emnyeca/emiuet/firmware/main/midi_out_uart_trs.c

#include "midi_out.h"

#include <stddef.h>

#include "board_pins.h"
#include "sdkconfig.h"

/* Defensive defaults for newly introduced Kconfig symbols.
 * This prevents build failures when the build directory has a stale sdkconfig.h.
 * Defaults must match Kconfig.projbuild.
 */
#ifndef CONFIG_EMIUET_MIDI_TRS_UART_ENABLE
#define CONFIG_EMIUET_MIDI_TRS_UART_ENABLE 0
#endif

#ifndef CONFIG_EMIUET_MIDI_TRS_IN_ENABLE
#define CONFIG_EMIUET_MIDI_TRS_IN_ENABLE 0
#endif

#ifndef CONFIG_EMIUET_MIDI_TASK_TRS_PRIORITY
#define CONFIG_EMIUET_MIDI_TASK_TRS_PRIORITY 7
#endif

#ifndef CONFIG_EMIUET_MIDI_TRS_QUEUE_LEN
#define CONFIG_EMIUET_MIDI_TRS_QUEUE_LEN 64
#endif

#include "esp_log.h"

#include "driver/uart.h"
#include "freertos/FreeRTOS.h"
#include "freertos/task.h"
#include "freertos/queue.h"
#include "midi_input.h"

static const char *TAG = "midi_out_uart_trs";

/*
 * TRS MIDI (Type-A) backend
 *
 * - UART: 31250 bps, 8-N-1
 * - Hardware is responsible for MIDI electrical compliance.
 *
 * Rev.B maps both Type-A TRS directions to UART1 through the GPIO matrix.
 */

#define MIDI_TRS_UART_PORT       UART_NUM_1
#define MIDI_TRS_UART_BAUDRATE   31250

#define MIDI_TRS_COALESCE_CHANNELS 16

typedef struct {
    uint8_t len;
    uint8_t bytes[3];
} midi_tx_item_t;

static bool s_inited = false;
static bool s_enabled = false;
static QueueHandle_t s_q = NULL;
static TaskHandle_t s_task = NULL;
static TaskHandle_t s_rx_task = NULL;
static midi_input_parser_t s_rx_parser;
static portMUX_TYPE s_coalesce_mux = portMUX_INITIALIZER_UNLOCKED;

/* Coalesce state (per-channel) */
static bool s_pb_pending[MIDI_TRS_COALESCE_CHANNELS] = {0};
static uint8_t s_pb_lsb[MIDI_TRS_COALESCE_CHANNELS] = {0};
static uint8_t s_pb_msb[MIDI_TRS_COALESCE_CHANNELS] = {0};

static bool s_cc1_pending[MIDI_TRS_COALESCE_CHANNELS] = {0};
static uint8_t s_cc1_val[MIDI_TRS_COALESCE_CHANNELS] = {0};

/* Stats */
static uint32_t s_drop_queue = 0;
static uint32_t s_drop_write = 0;
static uint32_t s_coalesce_pb = 0;
static uint32_t s_coalesce_cc1 = 0;
static uint32_t s_q_hwm = 0;
static TickType_t s_last_stats_log_tick = 0;

static inline void maybe_update_hwm(void)
{
    if (!s_q) return;
    const UBaseType_t used = uxQueueMessagesWaiting(s_q);
    if (used > s_q_hwm) s_q_hwm = (uint32_t)used;
}

static void maybe_log_stats(void)
{
    const TickType_t now = xTaskGetTickCount();
    const TickType_t interval = pdMS_TO_TICKS(1000);
    if (s_last_stats_log_tick != 0 && (now - s_last_stats_log_tick) < interval) return;

    if (s_drop_queue || s_drop_write || s_coalesce_pb || s_coalesce_cc1) {
        ESP_LOGW(TAG,
                 "stats q_hwm=%lu drop{q=%lu write=%lu} coalesce{pb=%lu cc1=%lu}",
                 (unsigned long)s_q_hwm,
                 (unsigned long)s_drop_queue,
                 (unsigned long)s_drop_write,
                 (unsigned long)s_coalesce_pb,
                 (unsigned long)s_coalesce_cc1);
    }
    s_last_stats_log_tick = now;
}

static inline bool is_pitchbend_3(const uint8_t *b, size_t len)
{
    return (len == 3) && ((b[0] & 0xF0u) == 0xE0u);
}

static inline bool is_cc1_3(const uint8_t *b, size_t len)
{
    return (len == 3) && ((b[0] & 0xF0u) == 0xB0u) && ((b[1] & 0x7Fu) == 1u);
}

static bool trs_uart_write_bytes(const uint8_t *bytes, size_t len)
{
    if (!bytes || len == 0) return false;
    int written = uart_write_bytes(MIDI_TRS_UART_PORT, (const char *)bytes, len);
    return written == (int)len;
}

static void trs_flush_coalesced_once(void)
{
    /* Flush coalesced continuous values. We keep this bounded and quick. */
    for (int ch = 0; ch < MIDI_TRS_COALESCE_CHANNELS; ++ch) {
        bool pb = false;
        uint8_t pb_lsb = 0;
        uint8_t pb_msb = 0;

        portENTER_CRITICAL(&s_coalesce_mux);
        pb = s_pb_pending[ch];
        if (pb) {
            pb_lsb = s_pb_lsb[ch];
            pb_msb = s_pb_msb[ch];
            s_pb_pending[ch] = false;
        }
        portEXIT_CRITICAL(&s_coalesce_mux);

        if (pb) {
            uint8_t b[3] = {(uint8_t)(0xE0u | (uint8_t)ch), pb_lsb, pb_msb};
            if (!trs_uart_write_bytes(b, sizeof(b))) {
                s_drop_write++;
            }
        }

        bool cc1 = false;
        uint8_t cc1_v = 0;

        portENTER_CRITICAL(&s_coalesce_mux);
        cc1 = s_cc1_pending[ch];
        if (cc1) {
            cc1_v = s_cc1_val[ch];
            s_cc1_pending[ch] = false;
        }
        portEXIT_CRITICAL(&s_coalesce_mux);

        if (cc1) {
            uint8_t b[3] = {(uint8_t)(0xB0u | (uint8_t)ch), 1u, (uint8_t)(cc1_v & 0x7Fu)};
            if (!trs_uart_write_bytes(b, sizeof(b))) {
                s_drop_write++;
            }
        }
    }
}

/* Producers publish (enqueue or coalesce) before notifying. The sender drains
 * everything before waiting again, so a notification given during a drain stays
 * pending and the next wait returns at once: no wakeup is lost.
 */
static inline void trs_tx_wake(void)
{
    TaskHandle_t task = s_task;
    if (task) xTaskNotifyGive(task);
}

static void trs_sender_task(void *arg)
{
    (void)arg;

    /* We intentionally do not call uart_wait_tx_done() per message.
     * UART driver TX buffer + this dedicated task provides stable latency.
     * uart_write_bytes() waits for ring-buffer space, so there is no retry state.
     */
    const int FLUSH_EVERY_N_EVENTS = 8;

    for (;;) {
        int sent_since_flush = 0;
        midi_tx_item_t item = {0};

        /* Single sender task owns the UART; no mutex required. */
        while (s_q && xQueueReceive(s_q, &item, 0) == pdTRUE) {
            maybe_update_hwm();
            if (!trs_uart_write_bytes(item.bytes, item.len)) {
                s_drop_write++;
            }
            if (++sent_since_flush >= FLUSH_EVERY_N_EVENTS) {
                sent_since_flush = 0;
                trs_flush_coalesced_once();
            }
        }

        /* Queue empty: flush continuous updates promptly, then sleep until notified. */
        trs_flush_coalesced_once();
        maybe_log_stats();
        (void)ulTaskNotifyTake(pdTRUE, portMAX_DELAY);
    }
}

static void trs_receiver_task(void *arg)
{
    (void)arg;
    uint8_t data[64];
    for (;;) {
        const int count = uart_read_bytes(MIDI_TRS_UART_PORT, data, sizeof(data),
                                          pdMS_TO_TICKS(20));
        if (count > 0) midi_input_feed(&s_rx_parser, data, (size_t)count);
    }
}

bool midi_out_uart_trs_init(void)
{
    if (s_inited) return s_enabled;
    s_inited = true;

#if !CONFIG_EMIUET_MIDI_TRS_UART_ENABLE
    s_enabled = false;
    ESP_LOGI(TAG, "TRS UART backend disabled (CONFIG_EMIUET_MIDI_TRS_UART_ENABLE=n)");
    return false;
#else

    uart_config_t cfg = {
        .baud_rate = MIDI_TRS_UART_BAUDRATE,
        .data_bits = UART_DATA_8_BITS,
        .parity = UART_PARITY_DISABLE,
        .stop_bits = UART_STOP_BITS_1,
        .flow_ctrl = UART_HW_FLOWCTRL_DISABLE,
        .source_clk = UART_SCLK_DEFAULT,
    };

    esp_err_t err = uart_param_config(MIDI_TRS_UART_PORT, &cfg);
    if (err != ESP_OK) {
        s_enabled = false;
        ESP_LOGE(TAG, "uart_param_config failed: %s", esp_err_to_name(err));
        return false;
    }

    err = uart_set_pin(MIDI_TRS_UART_PORT,
                       (int)PIN_MIDI_OUT_TX,
                       CONFIG_EMIUET_MIDI_TRS_IN_ENABLE ? (int)PIN_MIDI_IN_RX : UART_PIN_NO_CHANGE,
                       UART_PIN_NO_CHANGE,
                       UART_PIN_NO_CHANGE);
    if (err != ESP_OK) {
        s_enabled = false;
        ESP_LOGE(TAG, "uart_set_pin failed: %s", esp_err_to_name(err));
        return false;
    }

    /* A single UART driver owns both isolated MIDI IN and compliant MIDI OUT. */
    err = uart_driver_install(MIDI_TRS_UART_PORT, 256, 512, 0, NULL, 0);
    if (err != ESP_OK) {
        s_enabled = false;
        ESP_LOGE(TAG, "uart_driver_install failed: %s", esp_err_to_name(err));
        return false;
    }

    s_q = xQueueCreate(CONFIG_EMIUET_MIDI_TRS_QUEUE_LEN, sizeof(midi_tx_item_t));
    if (s_q == NULL) {
        s_enabled = false;
        ESP_LOGE(TAG, "failed to create queue");
        return false;
    }

    if (s_task == NULL) {
        BaseType_t ok = xTaskCreatePinnedToCore(trs_sender_task,
                                               "midi_trs_tx",
                                               4096,
                                               NULL,
                                               CONFIG_EMIUET_MIDI_TASK_TRS_PRIORITY,
                                               &s_task,
                                               0);
        if (ok != pdPASS) {
            s_task = NULL;
            s_enabled = false;
            ESP_LOGE(TAG, "failed to create sender task");
            return false;
        }
    }

#if CONFIG_EMIUET_MIDI_TRS_IN_ENABLE
    midi_input_parser_init(&s_rx_parser);
    if (s_rx_task == NULL) {
        BaseType_t ok = xTaskCreatePinnedToCore(trs_receiver_task,
                                               "midi_trs_rx",
                                               3072,
                                               NULL,
                                               CONFIG_EMIUET_MIDI_TASK_TRS_PRIORITY,
                                               &s_rx_task,
                                               0);
        if (ok != pdPASS) {
            ESP_LOGE(TAG, "failed to create receiver task");
            return false;
        }
    }
#endif

    s_enabled = true;
    ESP_LOGI(TAG, "TRS UART backend initialized (port=%d tx=%d rx=%d baud=%d)",
             (int)MIDI_TRS_UART_PORT, (int)PIN_MIDI_OUT_TX,
             CONFIG_EMIUET_MIDI_TRS_IN_ENABLE ? (int)PIN_MIDI_IN_RX : -1,
             (int)MIDI_TRS_UART_BAUDRATE);
    return true;
#endif
}

bool midi_out_uart_trs_send_bytes(const uint8_t *bytes, size_t len)
{
    if (!s_enabled) return false;
    if (!bytes || len == 0) return false;

    /* Coalesce continuous controllers to prevent queue saturation. */
    if (is_pitchbend_3(bytes, len)) {
        const uint8_t ch = (uint8_t)(bytes[0] & 0x0Fu);
        portENTER_CRITICAL(&s_coalesce_mux);
        if (s_pb_pending[ch]) s_coalesce_pb++;
        s_pb_pending[ch] = true;
        s_pb_lsb[ch] = (uint8_t)(bytes[1] & 0x7Fu);
        s_pb_msb[ch] = (uint8_t)(bytes[2] & 0x7Fu);
        portEXIT_CRITICAL(&s_coalesce_mux);
        trs_tx_wake();
        return true;
    }

    if (is_cc1_3(bytes, len)) {
        const uint8_t ch = (uint8_t)(bytes[0] & 0x0Fu);
        portENTER_CRITICAL(&s_coalesce_mux);
        if (s_cc1_pending[ch]) s_coalesce_cc1++;
        s_cc1_pending[ch] = true;
        s_cc1_val[ch] = (uint8_t)(bytes[2] & 0x7Fu);
        portEXIT_CRITICAL(&s_coalesce_mux);
        trs_tx_wake();
        return true;
    }

    if (!s_q) return false;
    midi_tx_item_t item = {0};
    item.len = (uint8_t)((len > 3) ? 3 : len);
    for (size_t i = 0; i < item.len; ++i) item.bytes[i] = bytes[i];

    if (xQueueSendToBack(s_q, &item, 0) != pdTRUE) {
        s_drop_queue++;
        maybe_update_hwm();
        trs_tx_wake();
        return false;
    }

    maybe_update_hwm();
    trs_tx_wake();
    return true;
}
