emnyeca/emiuet/firmware/main/midi_out_usb.c

#include "midi_out.h"

#include <stddef.h>
#include <string.h>

#include "esp_log.h"
#include "input_router.h"
#include "midi_input.h"
#include "usb_hid_keyboard.h"
#include "usb_power.h"

/* Defensive defaults for newly introduced Kconfig symbols.
 * This prevents build failures when the build directory has a stale sdkconfig.h.
 * Defaults must match Kconfig.projbuild.
 */
#ifndef CONFIG_EMIUET_MIDI_USB_QUEUE_LEN
#define CONFIG_EMIUET_MIDI_USB_QUEUE_LEN 1024
#endif

#ifndef CONFIG_EMIUET_MIDI_TASK_USB_PRIORITY
#define CONFIG_EMIUET_MIDI_TASK_USB_PRIORITY 6
#endif

#include "freertos/FreeRTOS.h"
#include "freertos/task.h"
#include "freertos/queue.h"
#include "freertos/semphr.h"

static const char *TAG = "midi_out_usb";

/*
 * Fixed-role USB Device backend
 *
 * This is intentionally isolated behind a config gate so the project
 * still builds even when TinyUSB is not enabled in sdkconfig.
 */
#if defined(CONFIG_TINYUSB_MIDI_COUNT) && (CONFIG_TINYUSB_MIDI_COUNT > 0)

#include "tinyusb.h"
#include "tinyusb_default_config.h"
#include "tusb.h"
#include "class/midi/midi_device.h"

/* Some TinyUSB versions (including the one bundled via ESP-IDF 5.3.x managed component)
 * don't provide tud_midi_ready(). Provide a local shim so we can log the state using the
 * name requested, without changing descriptors or the send path.
 */
static inline bool tud_midi_ready(void)
{
    return tud_midi_mounted();
}

#ifndef EMUIET_USB_MIDI_VID
#define EMUIET_USB_MIDI_VID 0x303A /* Espressif VID (commonly used in examples) */
#endif

#ifndef EMUIET_USB_MIDI_PID
#define EMUIET_USB_MIDI_PID 0x4005
#endif

#ifndef EMUIET_USB_MIDI_BCD
#define EMUIET_USB_MIDI_BCD 0x0101
#endif

/* USB descriptors */
static const tusb_desc_device_t s_desc_device = {
    .bLength = sizeof(tusb_desc_device_t),
    .bDescriptorType = TUSB_DESC_DEVICE,
    .bcdUSB = 0x0200,

    .bDeviceClass = 0x00,
    .bDeviceSubClass = 0x00,
    .bDeviceProtocol = 0x00,

    /* 64B is valid for Full Speed EP0 and avoids relying on tusb_config.h */
    .bMaxPacketSize0 = 64,

    .idVendor = EMUIET_USB_MIDI_VID,
    .idProduct = EMUIET_USB_MIDI_PID,
    .bcdDevice = EMUIET_USB_MIDI_BCD,

    .iManufacturer = 0x01,
    .iProduct = 0x02,
    .iSerialNumber = 0x03,

    .bNumConfigurations = 0x01,
};

/* Strings must remain in flash/ROM */
static const char *s_string_desc[] = {
    (const char[]){0x09, 0x04}, /* 0: English (0x0409) */
    "Emnyeca",
    "Emiuet MIDI + Keyboard",
    "0001",
    "Emiuet Keyboard",
};

/*
 * Configuration descriptor:
 * - One configuration
 * - MIDI 1.0 function (Audio Control + MIDI Streaming interfaces)
 * - HID boot keyboard interface
 */
#define EMUIET_USB_ITF_NUM_MIDI 0
#define EMUIET_USB_ITF_NUM_HID  2
#define EMUIET_USB_ITF_NUM_TOTAL 3

#define EMUIET_USB_EP_MIDI_OUT 0x01
#define EMUIET_USB_EP_MIDI_IN  0x81
#define EMUIET_USB_EP_HID_IN   0x82

#ifndef EMUIET_USB_MIDI_EP_SIZE
#define EMUIET_USB_MIDI_EP_SIZE 64
#endif

#ifndef EMUIET_USB_HID_EP_SIZE
#define EMUIET_USB_HID_EP_SIZE 8
#endif

static const uint8_t s_hid_report_descriptor[] = {
    TUD_HID_REPORT_DESC_KEYBOARD()
};

static const uint8_t s_desc_configuration[] = {
    TUD_CONFIG_DESCRIPTOR(1, EMUIET_USB_ITF_NUM_TOTAL, 0,
                          (TUD_CONFIG_DESC_LEN + TUD_MIDI_DESC_LEN + TUD_HID_DESC_LEN),
                          0x00, 500),
    /* Note: TUD_MIDI_DESCRIPTOR signature depends on TinyUSB version. In esp-idf v5.3.4's tinyusb, it is:
     *   TUD_MIDI_DESCRIPTOR(itfnum, stridx, epout, epin, epsize)
     * We don't provide a dedicated interface string, so stridx=0.
     */
    TUD_MIDI_DESCRIPTOR(EMUIET_USB_ITF_NUM_MIDI, 0, EMUIET_USB_EP_MIDI_OUT, EMUIET_USB_EP_MIDI_IN, EMUIET_USB_MIDI_EP_SIZE),
    TUD_HID_DESCRIPTOR(EMUIET_USB_ITF_NUM_HID, 4, HID_ITF_PROTOCOL_KEYBOARD,
                       sizeof(s_hid_report_descriptor), EMUIET_USB_EP_HID_IN,
                       EMUIET_USB_HID_EP_SIZE, 10)
};

static bool s_inited = false;
static midi_input_parser_t s_midi_rx_parser;
static TaskHandle_t s_usb_state_task_handle = NULL;

typedef struct {
    uint8_t len;
    uint8_t bytes[3];
} midi_tx_item_t;

static QueueHandle_t s_usb_q = NULL;
static TaskHandle_t s_usb_tx_task_handle = NULL;
static portMUX_TYPE s_usb_coalesce_mux = portMUX_INITIALIZER_UNLOCKED;

static bool s_usb_pb_pending[16] = {0};
static uint8_t s_usb_pb_lsb[16] = {0};
static uint8_t s_usb_pb_msb[16] = {0};

static bool s_usb_cc1_pending[16] = {0};
static uint8_t s_usb_cc1_val[16] = {0};

static uint32_t s_usb_drop_queue = 0;
static uint32_t s_usb_drop_write = 0;
static uint32_t s_usb_coalesce_pb = 0;
static uint32_t s_usb_coalesce_cc1 = 0;
static uint32_t s_usb_q_hwm = 0;
static TickType_t s_usb_last_stats_log_tick = 0;

uint8_t const *tud_hid_descriptor_report_cb(uint8_t instance)
{
    (void)instance;
    return s_hid_report_descriptor;
}

void tud_midi_rx_cb(uint8_t instance)
{
    (void)instance;
    uint8_t bytes[64];
    while (tud_midi_available()) {
        const uint32_t count = tud_midi_stream_read(bytes, sizeof(bytes));
        if (count == 0) break;
        midi_input_feed(&s_midi_rx_parser, bytes, count);
    }
}

uint16_t tud_hid_get_report_cb(uint8_t instance, uint8_t report_id,
                               hid_report_type_t report_type, uint8_t *buffer,
                               uint16_t reqlen)
{
    (void)instance;
    (void)report_id;
    (void)report_type;
    (void)buffer;
    (void)reqlen;
    return 0;
}

void tud_hid_set_report_cb(uint8_t instance, uint8_t report_id,
                           hid_report_type_t report_type,
                           uint8_t const *buffer, uint16_t bufsize)
{
    (void)instance;
    (void)report_id;
    if (report_type == HID_REPORT_TYPE_OUTPUT && buffer && bufsize > 0) {
        usb_hid_keyboard_set_led_report(buffer[0]);
    }
}

static void usb_clear_pending_midi(void)
{
    if (s_usb_q) (void)xQueueReset(s_usb_q);
    portENTER_CRITICAL(&s_usb_coalesce_mux);
    memset(s_usb_pb_pending, 0, sizeof(s_usb_pb_pending));
    memset(s_usb_cc1_pending, 0, sizeof(s_usb_cc1_pending));
    portEXIT_CRITICAL(&s_usb_coalesce_mux);
}

static inline void usb_maybe_update_hwm(void)
{
    if (!s_usb_q) return;
    const UBaseType_t used = uxQueueMessagesWaiting(s_usb_q);
    if (used > s_usb_q_hwm) s_usb_q_hwm = (uint32_t)used;
}

static void usb_maybe_log_stats(void)
{
    const TickType_t now = xTaskGetTickCount();
    const TickType_t interval = pdMS_TO_TICKS(1000);
    if (s_usb_last_stats_log_tick != 0 && (now - s_usb_last_stats_log_tick) < interval) return;

    if (s_usb_drop_queue || s_usb_drop_write || s_usb_coalesce_pb || s_usb_coalesce_cc1) {
        ESP_LOGW(TAG,
                 "stats q_hwm=%lu drop{q=%lu write=%lu} coalesce{pb=%lu cc1=%lu}",
                 (unsigned long)s_usb_q_hwm,
                 (unsigned long)s_usb_drop_queue,
                 (unsigned long)s_usb_drop_write,
                 (unsigned long)s_usb_coalesce_pb,
                 (unsigned long)s_usb_coalesce_cc1);
    }
    s_usb_last_stats_log_tick = now;
}

static inline bool is_pitchbend_3(const uint8_t *b, size_t len)
{
    return (len == 3) && ((b[0] & 0xF0u) == 0xE0u);
}

static inline bool is_cc1_3(const uint8_t *b, size_t len)
{
    return (len == 3) && ((b[0] & 0xF0u) == 0xB0u) && ((b[1] & 0x7Fu) == 1u);
}

static bool usb_send_lowlevel(const uint8_t *bytes, size_t len)
{
    if (!s_inited) return false;
    if (!bytes || len == 0) return false;
    if (!tud_mounted()) return false;

    uint32_t written = tud_midi_stream_write(0, bytes, (uint32_t)len);
    return written == len;
}

/* Producers publish (enqueue or coalesce) before notifying. The sender drains
 * everything before waiting again, so a notification given during a drain stays
 * pending and the next wait returns at once: no wakeup is lost.
 */
static inline void usb_tx_wake(void)
{
    TaskHandle_t task = s_usb_tx_task_handle;
    if (task) xTaskNotifyGive(task);
}

/* Returns false when TinyUSB could not accept a value; it stays pending. */
static bool usb_flush_coalesced_once(void)
{
    for (int ch = 0; ch < 16; ++ch) {
        bool pb = false;
        uint8_t pb_lsb = 0;
        uint8_t pb_msb = 0;

        portENTER_CRITICAL(&s_usb_coalesce_mux);
        pb = s_usb_pb_pending[ch];
        if (pb) {
            pb_lsb = s_usb_pb_lsb[ch];
            pb_msb = s_usb_pb_msb[ch];
            s_usb_pb_pending[ch] = false;
        }
        portEXIT_CRITICAL(&s_usb_coalesce_mux);

        if (pb) {
            uint8_t b[3] = {(uint8_t)(0xE0u | (uint8_t)ch), pb_lsb, pb_msb};
            if (!usb_send_lowlevel(b, sizeof(b))) {
                /* Keep pending on failure to avoid losing latest value. */
                portENTER_CRITICAL(&s_usb_coalesce_mux);
                /* A producer may have published a newer value during I/O. */
                if (!s_usb_pb_pending[ch]) {
                    s_usb_pb_pending[ch] = true;
                    s_usb_pb_lsb[ch] = pb_lsb;
                    s_usb_pb_msb[ch] = pb_msb;
                }
                portEXIT_CRITICAL(&s_usb_coalesce_mux);
                s_usb_drop_write++;
                return false;
            }
        }

        bool cc1 = false;
        uint8_t cc1_v = 0;

        portENTER_CRITICAL(&s_usb_coalesce_mux);
        cc1 = s_usb_cc1_pending[ch];
        if (cc1) {
            cc1_v = s_usb_cc1_val[ch];
            s_usb_cc1_pending[ch] = false;
        }
        portEXIT_CRITICAL(&s_usb_coalesce_mux);

        if (cc1) {
            uint8_t b[3] = {(uint8_t)(0xB0u | (uint8_t)ch), 1u, (uint8_t)(cc1_v & 0x7Fu)};
            if (!usb_send_lowlevel(b, sizeof(b))) {
                portENTER_CRITICAL(&s_usb_coalesce_mux);
                if (!s_usb_cc1_pending[ch]) {
                    s_usb_cc1_pending[ch] = true;
                    s_usb_cc1_val[ch] = cc1_v;
                }
                portEXIT_CRITICAL(&s_usb_coalesce_mux);
                s_usb_drop_write++;
                return false;
            }
        }
    }
    return true;
}

/* Sends queued discrete events in order, interleaving the coalesced values every
 * USB_FLUSH_EVERY_N_EVENTS and after the queue empties. Returns false if TinyUSB
 * refused data (TX FIFO full or not mounted); that data stays pending.
 * A refused 1-3 byte message is not partially written: TinyUSB checks for a free
 * 4-byte packet before consuming any byte, and this task is the only writer.
 */
#define USB_FLUSH_EVERY_N_EVENTS 16

static bool usb_tx_drain(int *sent_since_flush)
{
    midi_tx_item_t item = {0};
    while (s_usb_q && xQueuePeek(s_usb_q, &item, 0) == pdTRUE) {
        /* Preserve the interleave deadline across FIFO-full retries. */
        if (*sent_since_flush >= USB_FLUSH_EVERY_N_EVENTS) {
            if (!usb_flush_coalesced_once()) return false;
            *sent_since_flush = 0;
        }
        usb_maybe_update_hwm();
        if (!usb_send_lowlevel(item.bytes, item.len)) {
            s_usb_drop_write++;
            return false;
        }
        (void)xQueueReceive(s_usb_q, &item, 0);
        ++*sent_since_flush;
    }
    if (!usb_flush_coalesced_once()) return false;
    *sent_since_flush = 0;
    return true;
}

/* On refusal, actually block for a tick so the lower-priority TinyUSB task can
 * free TX space. Producer notifications must not bypass this scheduling break.
 */
#define USB_TX_RETRY_TICKS (pdMS_TO_TICKS(1) ? pdMS_TO_TICKS(1) : (TickType_t)1)

static void midi_out_usb_tx_task(void *arg)
{
    (void)arg;
    int sent_since_flush = 0;
    for (;;) {
        const bool drained = usb_tx_drain(&sent_since_flush);
        usb_maybe_log_stats();
        if (drained) {
            (void)ulTaskNotifyTake(pdTRUE, portMAX_DELAY);
        } else {
            vTaskDelay(USB_TX_RETRY_TICKS);
        }
    }
}

static void midi_out_usb_event_cb(tinyusb_event_t *event, void *arg)
{
    (void)arg;
    if (!event) return;

    switch (event->id) {
        case TINYUSB_EVENT_ATTACHED:
            /* Only the state monitor grants Default-current RGB power, so a
             * failed monitor task cannot leave an unmonitored grant active. */
            ESP_LOGI(TAG, "tud_mount_cb(): tud_mounted()=%d tud_midi_ready()=%d", (int)tud_mounted(), (int)tud_midi_ready());
            usb_tx_wake();
            break;
        case TINYUSB_EVENT_DETACHED:
            ESP_LOGI(TAG, "tud_umount_cb(): tud_mounted()=%d tud_midi_ready()=%d", (int)tud_mounted(), (int)tud_midi_ready());
            usb_clear_pending_midi();
            usb_hid_keyboard_disconnected();
            input_router_usb_disconnected();
            break;
        default:
            break;
    }
}

static void midi_out_usb_state_task(void *arg)
{
    (void)arg;

    bool last_mounted = false;
    bool last_ready = false;

    while (1) {
        const bool mounted = tud_mounted();
        usb_power_set_bus_state(mounted, tud_suspended());
        const bool ready = mounted && tud_midi_ready();

        if (mounted != last_mounted) {
            ESP_LOGI(TAG, "tud_mounted() -> %d", (int)mounted);
            last_mounted = mounted;
            /* Also covers a missed ATTACHED event; the sender then retries pending data. */
            usb_tx_wake();
        }

        if (ready != last_ready) {
            ESP_LOGI(TAG, "tud_midi_ready() -> %d", (int)ready);
            last_ready = ready;
        }

        /* Short delay to avoid busy looping.
         * Note: the actual TinyUSB stack is serviced by esp_tinyusb's own task (tud_task()).
         */
        vTaskDelay(pdMS_TO_TICKS(10));
    }
}

bool midi_out_usb_init(void)
{
    if (s_inited) return true;

    /* TODO (prototype bring-up):
     * On some ESP32-S3 DevKits, the USB connector used for flashing/monitoring is USB-Serial/JTAG,
     * not the native USB D+/D- (PIN_USB_D_PLUS/PIN_USB_D_MINUS). In that case Windows won't enumerate this
     * TinyUSB composite Device and tud_mount_cb()/tud_mounted() won't fire.
     * Ensure the cable is on the native USB Device port when validating enumeration.
     */

    /* Rev.B is bus-powered from this same connector. The CC comparator
     * (usb_cc_detect) observes the Type-C current advertisement independently.
     */
    tinyusb_config_t cfg = TINYUSB_DEFAULT_CONFIG();
    cfg.descriptor.device = &s_desc_device;
    cfg.descriptor.string = s_string_desc;
    cfg.descriptor.full_speed_config = s_desc_configuration;
#if (TUD_OPT_HIGH_SPEED)
    cfg.descriptor.high_speed_config = s_desc_configuration;
#endif

    /* Ensure the TinyUSB stack task (which runs tud_task() in a loop) is pinned to CPU0.
     * This keeps USB enumeration progressing even after app_main() returns.
     */
    cfg.task.xCoreID = 0;
    cfg.task.priority = 5;
    cfg.event_cb = midi_out_usb_event_cb;
    cfg.event_arg = NULL;

    midi_input_parser_init(&s_midi_rx_parser);
    esp_err_t err = tinyusb_driver_install(&cfg);
    if (err != ESP_OK) {
        ESP_LOGE(TAG, "tinyusb_driver_install failed: %s", esp_err_to_name(err));
        return false;
    }

    if (s_usb_state_task_handle == NULL) {
        BaseType_t ok = xTaskCreatePinnedToCore(midi_out_usb_state_task,
                                               "usb_state",
                                               2048,
                                               NULL,
                                               5,
                                               &s_usb_state_task_handle,
                                               0);
        if (ok != pdPASS) {
            s_usb_state_task_handle = NULL;
            ESP_LOGW(TAG, "Failed to start USB state monitor task");
        }
    }

    s_inited = true;
    if (!usb_hid_keyboard_init()) {
        ESP_LOGE(TAG, "failed to initialize USB HID keyboard sender");
    }
    ESP_LOGI(TAG, "USB MIDI + HID composite backend initialized");

    if (s_usb_q == NULL) {
        s_usb_q = xQueueCreate(CONFIG_EMIUET_MIDI_USB_QUEUE_LEN, sizeof(midi_tx_item_t));
        if (s_usb_q == NULL) {
            ESP_LOGE(TAG, "failed to create USB MIDI queue");
            return true;
        }
    }

    if (s_usb_tx_task_handle == NULL) {
        BaseType_t ok = xTaskCreatePinnedToCore(midi_out_usb_tx_task,
                                               "midi_usb_tx",
                                               4096,
                                               NULL,
                                               CONFIG_EMIUET_MIDI_TASK_USB_PRIORITY,
                                               &s_usb_tx_task_handle,
                                               0);
        if (ok != pdPASS) {
            s_usb_tx_task_handle = NULL;
            ESP_LOGW(TAG, "failed to create USB MIDI sender task");
        }
    }

    return true;
}

bool midi_out_usb_send_bytes(const uint8_t *bytes, size_t len)
{
    if (!s_inited) return false;
    if (!bytes || len == 0) return false;

    /* Never replay notes performed while the USB host was absent. */
    if (!tud_mounted()) return false;

    /* Coalesce continuous controllers to prevent queue saturation. */
    if (is_pitchbend_3(bytes, len)) {
        const uint8_t ch = (uint8_t)(bytes[0] & 0x0Fu);
        portENTER_CRITICAL(&s_usb_coalesce_mux);
        if (s_usb_pb_pending[ch]) s_usb_coalesce_pb++;
        s_usb_pb_pending[ch] = true;
        s_usb_pb_lsb[ch] = (uint8_t)(bytes[1] & 0x7Fu);
        s_usb_pb_msb[ch] = (uint8_t)(bytes[2] & 0x7Fu);
        portEXIT_CRITICAL(&s_usb_coalesce_mux);
        usb_tx_wake();
        return true;
    }

    if (is_cc1_3(bytes, len)) {
        const uint8_t ch = (uint8_t)(bytes[0] & 0x0Fu);
        portENTER_CRITICAL(&s_usb_coalesce_mux);
        if (s_usb_cc1_pending[ch]) s_usb_coalesce_cc1++;
        s_usb_cc1_pending[ch] = true;
        s_usb_cc1_val[ch] = (uint8_t)(bytes[2] & 0x7Fu);
        portEXIT_CRITICAL(&s_usb_coalesce_mux);
        usb_tx_wake();
        return true;
    }

    if (!s_usb_q) {
        /* If init didn't create queue for some reason, fall back to direct send. */
        return usb_send_lowlevel(bytes, len);
    }

    midi_tx_item_t item = {0};
    item.len = (uint8_t)((len > 3) ? 3 : len);
    for (size_t i = 0; i < item.len; ++i) item.bytes[i] = bytes[i];

    if (xQueueSendToBack(s_usb_q, &item, 0) != pdTRUE) {
        s_usb_drop_queue++;
        usb_maybe_update_hwm();
        usb_tx_wake();
        return false;
    }

    usb_maybe_update_hwm();
    usb_tx_wake();
    return true;
}

#else

bool midi_out_usb_init(void)
{
    /* TinyUSB not enabled in sdkconfig; keep build working. */
    ESP_LOGW(TAG, "TinyUSB MIDI not enabled (CONFIG_TINYUSB_MIDI_COUNT=0); USB-MIDI backend disabled");
    return false;
}

bool midi_out_usb_send_bytes(const uint8_t *bytes, size_t len)
{
    (void)bytes;
    (void)len;
    return false;
}

#endif
